Entropy98/corneds/firmware/inc/keymap.h

/*
 * \file keymap.h
 * \author Harper Weigle
 * \date Dec 18 2023
 * \brief mapping of keys to functions
 */

#ifndef _INC_KEYMAP_H
#define _INC_KEYMAP_H

#include "pinmap.h"
#include "tusb.h"

#define MACRO_AMPERSAND         0xFF
#define MACRO_CARET             0xFE
#define MACRO_ASTRISK           0xFD
#define MACRO_PARENTHESIS_LEFT  0xFC
#define MACRO_PARENTHESIS_RIGHT 0xFB
#define MACRO_COLON             0xFA
#define MACRO_CURLY_LEFT        0xF9
#define MACRO_CURLY_RIGHT       0xF8
#define MACRO_PIPE              0xF7
#define MACRO_PLUS              0xF6
#define MACRO_EXCLAMATION_POINT 0xF5
#define MACRO_AT                0xF4
#define MACRO_HASHTAG           0xF3
#define MACRO_DOLLAR_SIGN       0xF2
#define MACRO_PERCENT           0xF1
#define MACRO_TILDE             0xF0
#define MACRO_LESS_THAN         0xEF
#define MACRO_GREATER_THAN      0xEE

#define ROW0_MASK (0x01 << KEYROW0_PIN)
#define ROW1_MASK (0x01 << KEYROW1_PIN)
#define ROW2_MASK (0x01 << KEYROW2_PIN)
#define ROW3_MASK (0x01 << KEYROW3_PIN)

#define NUM_COLS 6
#define NUM_ROWS 4
#define KEY_BUFFER_SIZE 50

#define ALTGUI_ROW     3
#define ALTGUI_COL     3
#define CTRL_ROW       1
#define CTRL_COL       0
#define ENTERSPACE_COL 5
#define ENTERSPACE_ROW 3
#define SHIFT_ROW      2
#define SHIFT_COL      0
#define MOD_ROW        3
#define MOD_COL        4

#define MOD_MASK_RIGHT 0x1
#define MOD_MASK_LEFT  0x2

#define KBDSIDE_RIGHT 1U
#define KBDSIDE_LEFT 2U

typedef uint8_t keymap_t[4][6];

void init_keys(bool is_main);
uint8_t kbd_side_get();
void poll_keypresses();
void push_keypress(uint8_t col, uint8_t row, bool is_right_side);
uint8_t get_keypress();
bool lowered_mod_get();
void lowered_mod_set(bool pressed);
uint8_t mod_get();
void mod_set(uint8_t mod);
void mod_unset(uint8_t mod);
bool raised_mod_get();
void raised_mod_set(bool pressed);
void unset_change_queued();

#endif //_INC_KEYMAP_H
