Entropy98/corneds/firmware/inc/led_utils.h

/*
 * \file led_utils.h
 * \author Harper Weigle
 * \date May 11 2023
 * \brief LED utilities
 */

#ifndef _INC_LED_UTILS_H
#define _INC_LED_UTILS_H

void led_init();
void led_off();
void led_on();
void led_toggle();

#endif //_INC_KEYMAP_H
